LeticiaAires/Gravity-Glitch/Assets/background.jpg

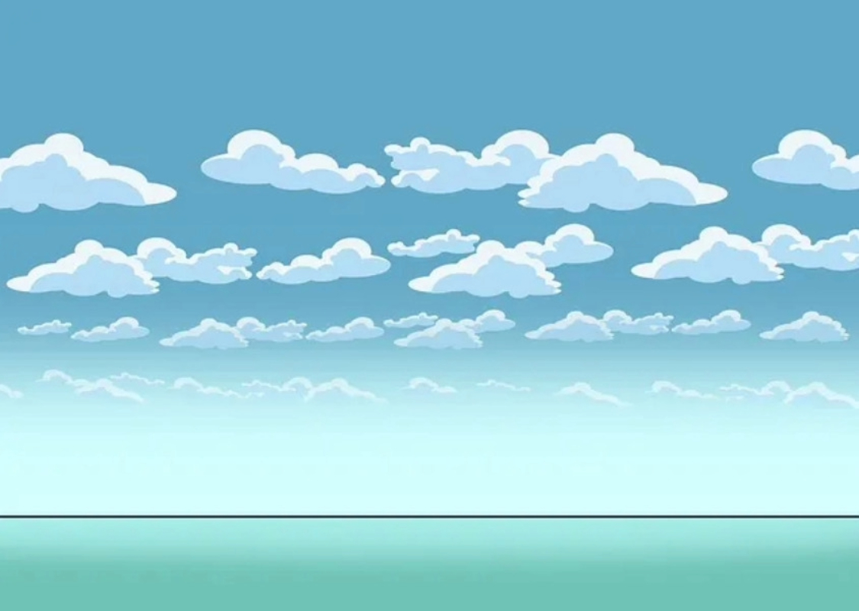
Assets/background.jpg
