LeticiaAires/Gravity-Glitch/Assets/chapeau_cowboy.png

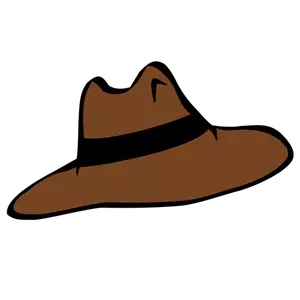
Assets/chapeau_cowboy.png
