LeticiaAires/Gravity-Glitch/Assets/ground.png

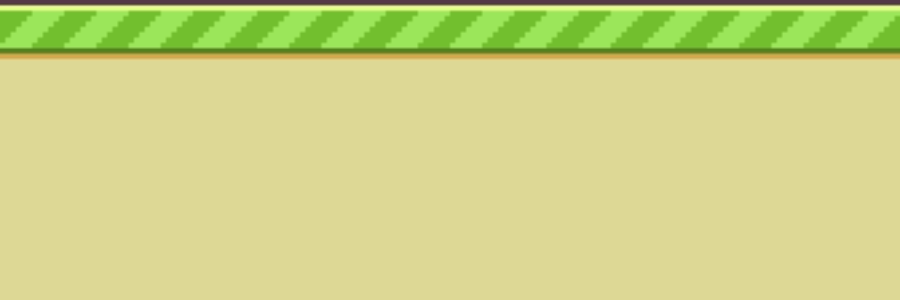
Assets/ground.png
