LeticiaAires/Gravity-Glitch/Assets/sound.png

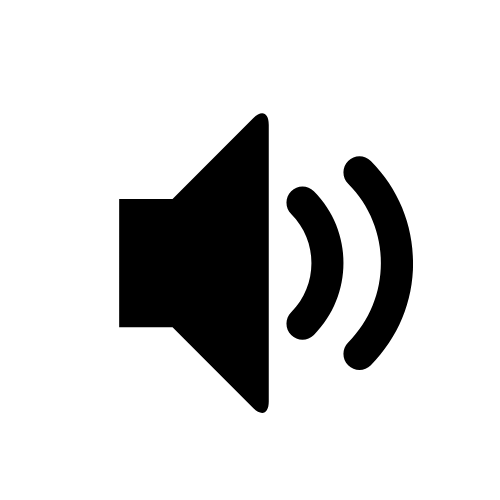
Assets/sound.png
