LeticiaAires/Gravity-Glitch/Assets/tuba.jpg

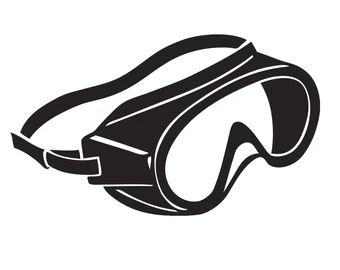
Assets/tuba.jpg
